smartboxchannel/EFEKTA-DOOR-WINDOW-SENSOR/IMAGES/2.jpeg

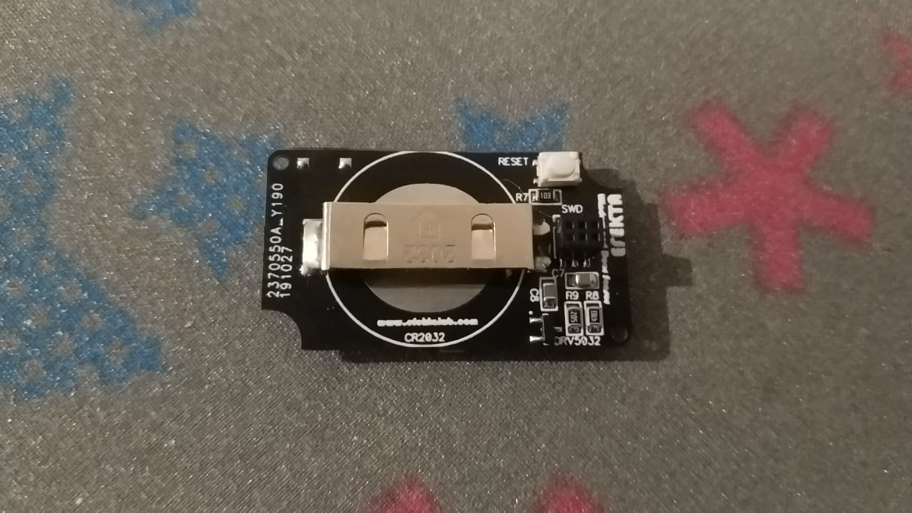
IMAGES/2.jpeg
